carterd/BTSpecializedDisplay/src/gui/BluetoothConnection.cpp

#include "BluetoothConnection.h"
#include "MonitorSelector.h"
#include "../themes/display_theme.h"

void BluetoothConnection::tile_changed_cb(lv_event_t* event) {
    ((BluetoothConnection*)(event->user_data))->tileChangedCB(event);
}

void BluetoothConnection::refresh_cb(lv_event_t* event) {
	((BluetoothConnection*)(event->user_data))->refreshCB(event);
}

void BluetoothConnection::exit_btn_cb(lv_event_t* event) {
    ((BluetoothConnection*)(event->user_data))->exitButtonCB(event);
}

void BluetoothConnection::lv_event_encorder_cb(lv_event_t* event) {
    ((BluetoothConnection*)(event->user_data))->encoderActivityCB(event);
}

void BluetoothConnection::connecting_timer_cb(lv_timer_t * timer) {
    ((BluetoothConnection*)(timer->user_data))->connectingTimerCB(timer);
}

BluetoothConnection::BluetoothConnection(BluetoothController* bluetoothController, ConfigStore* configStore, lv_img_dsc_t* image, lv_indev_t* indev, ButtonLabelBar* buttonLabelBar)  : ButtonLabelledLvObject(indev, buttonLabelBar)
{
    this->monitor_tile_obj = NULL;
	this->bluetoothController = bluetoothController;
	this->configStore = configStore;
	this->image = image;
    this->connectedBike = false;
    this->connectedHeartRateMonitor = false;
    this->monitorSelectorActive = false;
    this->monitorSelector = NULL;
    this->exiting = false;
    this->initialConnectionState = true;
    this->connectingIncludesHeartRateMonitorState = false;
}

BluetoothConnection::~BluetoothConnection()
{
    this->monitorSelector->destroyLvObj();
    //delete(this->monitorLvObj);
    BluetoothConnection::destroyLvObj();
}

lv_obj_t* BluetoothConnection::createLvObj(lv_obj_t* parent)
{
    // get the style we'll need for the bar
    display_theme_styles_t* display_theme_styles = (display_theme_styles_t*)lv_disp_get_theme(lv_obj_get_disp(parent))->user_data;
    lv_style_t* no_scrollbar_style = &(display_theme_styles->no_scrollbar);
    lv_style_t* button_no_highlight_style = &(display_theme_styles->button_no_highlight);
    lv_style_t* searching_button_style = &(display_theme_styles->searching_label);

    // create a group for the button for exit connection
    this->group = lv_group_create();

    lv_obj_update_layout(parent);    
    this->this_obj = lv_obj_create(parent);
    lv_obj_add_style(this->this_obj, no_scrollbar_style, LV_PART_SCROLLBAR);
    lv_obj_set_size(this->this_obj, lv_obj_get_width(parent), lv_obj_get_height(parent));
    lv_obj_set_align(this->this_obj, LV_ALIGN_CENTER);

    // The connection is created from a tileview
    this->tileview_obj = lv_tileview_create(this->this_obj);
    lv_obj_add_event_cb(this->tileview_obj, BluetoothConnection::tile_changed_cb, LV_EVENT_VALUE_CHANGED, this);
    lv_obj_add_style(tileview_obj, no_scrollbar_style, LV_PART_SCROLLBAR);
    this->connection_tile_obj = lv_tileview_add_tile(tileview_obj, 0, 0, LV_DIR_ALL);
    lv_obj_add_style(this->connection_tile_obj, no_scrollbar_style, LV_PART_SCROLLBAR);

    // Create a button
    this->button_obj = lv_btn_create(this->connection_tile_obj);
    lv_obj_center(this->button_obj);
    lv_obj_add_style(this->button_obj, button_no_highlight_style, LV_PART_MAIN);
    lv_obj_add_event_cb(this->button_obj, BluetoothConnection::refresh_cb, LV_EVENT_REFRESH, this);
    lv_obj_add_event_cb(this->button_obj, BluetoothConnection::exit_btn_cb, LV_EVENT_LONG_PRESSED, this);
    lv_obj_add_event_cb(this->button_obj, BluetoothConnection::lv_event_encorder_cb, LV_EVENT_CLICKED, this);
    lv_group_add_obj(this->group, this->button_obj);
    
    // add two activity button object to identify if encoder is being used
    lv_obj_t* activity_btn_1_obj = lv_btn_create(this->this_obj);
    lv_obj_add_style(activity_btn_1_obj, button_no_highlight_style, LV_PART_MAIN);
    lv_obj_add_event_cb(activity_btn_1_obj, BluetoothConnection::lv_event_encorder_cb, LV_EVENT_FOCUSED, this);
    lv_group_add_obj(this->group, activity_btn_1_obj);

    // Associate an image
    lv_obj_t* img_obj = lv_img_create(this->button_obj);
    lv_img_set_src(img_obj, this->image);
    lv_obj_center(img_obj);

    // Associate a spinner
    this->spinner_obj = lv_spinner_create(this->this_obj, 1000, 60);
    lv_obj_center(this->spinner_obj);

    // Associate a label connecting
    this->label_obj = lv_label_create(this->this_obj);
    lv_label_set_text(this->label_obj, SEARCHING_STRING);
    lv_obj_add_style(this->label_obj, searching_button_style, LV_PART_MAIN);
    lv_obj_center(this->label_obj);
    
    // create the monitor tile
    if (this->monitorSelector) {
        this->monitor_tile_obj = lv_tileview_add_tile(this->tileview_obj, 0, 1, LV_DIR_ALL);
        lv_obj_add_style(this->monitor_tile_obj, no_scrollbar_style, LV_PART_SCROLLBAR);
    }
    
    // Return the connection lv_obj just in case
    return this->this_obj;
}

void BluetoothConnection::destroyLvObj() {
    if (this->group) lv_group_del(this->group);
    this->group = NULL;
    BaseLvObject::destroyLvObj();
}

void BluetoothConnection::focusLvObj(BaseLvObject* defocusLvObj)
{
    this->updateButtonLabelBar();

    if (defocusLvObj) {
        // We have arrived here from an external lvObject so we're on the initial connection
        this->defocusLvObj = defocusLvObj;
        this->exiting = false;
        this->initialConnectionState = true;
        this->connectingIncludesHeartRateMonitorState = false;

        // Ensure the monitor selector is started
        this->monitorSelector->destroyLvObj();
        this->monitorSelector->createLvObj(this->monitor_tile_obj);

        // Ensure the connection view is shown if jumping to the connection
        lv_obj_set_tile_id(this->tileview_obj, 0, 0, LV_ANIM_OFF);
        // Capture movement from here on in
        lv_indev_set_group(this->indev, this->group);
        lv_group_focus_obj(this->button_obj);

        this->monitorSelectorActive = false;
        this->startBikeConnection();
        
    } else {
        // If we are already connecting and we get focus this is a reconnect due to disconnect
        this->initialConnectionState = false;
        // Ensure the connection view is shown if jumping to the connection
        lv_obj_set_tile_id(this->tileview_obj, 0, 0, LV_ANIM_OFF);
        // Capture movement from here on in
        lv_indev_set_group(this->indev, this->group);
        lv_group_focus_obj(this->button_obj);

        this->monitorSelectorActive = false;
        this->startBikeConnection();
    }
}

void BluetoothConnection::setMonitorSelector(MonitorSelector* monitorSelector)
{
    this->monitorSelector = monitorSelector;
    this->monitorSelector->setBluetoothConnection(this);
}

void BluetoothConnection::startBikeConnection()
{
    this->connectingStartTime = millis();
    this->connecting_timer = lv_timer_create(connecting_timer_cb, CONNECTING_TIMEOUT_MILLIS, this);
    // We should be in a disconnected state but ensure the bike is disconnected
    this->connectedBike = false;
    this->bluetoothController->getBluetoothBike()->disconnect();
    this->connectedHeartRateMonitor = this->bluetoothController->getBluetoothHeartRateMonitor()->isConnected();
    
    this->bluetoothController->startConnections(this->button_obj);

    lv_obj_clear_flag(this->label_obj, LV_OBJ_FLAG_HIDDEN);
    lv_obj_clear_flag(this->spinner_obj, LV_OBJ_FLAG_HIDDEN);
}

void BluetoothConnection::stopBTConnection()
{
    this->connectedBike = false;
    this->connectedHeartRateMonitor = false;
    this->bluetoothController->stopConnections();
}

void BluetoothConnection::restartBTConnection() {
    //this->startBTConnection();
    this->focusLvObj();
}


void BluetoothConnection::updateButtonLabelBar() {
    if (this->buttonLabelBar) {
        this->buttonLabelBar->setButtonLabels("", LV_SYMBOL_CLOSE, "");
        this->buttonLabelBar->setAutoHide(true);
        this->hideButtonLabels();
    }
}

void BluetoothConnection::showButtonLabels() {
    if (this->buttonLabelBar) {
        this->buttonLabelBar->show();
    }
}

void BluetoothConnection::hideButtonLabels()
{
	if (this->buttonLabelBar) {
		this->buttonLabelBar->hide();
	}
}

void BluetoothConnection::switchToMonitorLvObject()
{
    // Ensure the monitor screen is set up and move the gui to showing it
    if (this->monitorSelector) {
        this->monitorSelector->setBluetoothBike(this->bluetoothController->getBluetoothBike());
        this->monitorSelector->initBluetoothStats();
        this->monitorSelector->focusLvObj(this);
        lv_obj_set_tile_id(this->tileview_obj, 0, 1, LV_ANIM_ON);
        this->monitorSelectorActive = true;
    }
}

void BluetoothConnection::switchToConnectionLvObject()
{
    // Ensure the monitor screen is set up and move the gui to showing it
    if (this->monitorSelectorActive) {
        lv_obj_set_tile_id(this->tileview_obj, 0, 0, LV_ANIM_ON);
        this->monitorSelectorActive = false;
    }
}

void BluetoothConnection::connectionSuccess() 
{
    lv_obj_add_flag(this->label_obj, LV_OBJ_FLAG_HIDDEN);
    lv_obj_add_flag(this->spinner_obj, LV_OBJ_FLAG_HIDDEN);

    // On successful connection we should ensure the bike config is set correctly
    BikeConfig bikeConfig = this->configStore->getBikeConfig();

    if (bikeConfig.beeper.managed) this->bluetoothController->getBluetoothBike()->writeBikeStateAttribute(BikeStateAttributeIndex::BEEP_ON_OFF_STATE, &(bikeConfig.beeper.value));
    //if (bikeConfig.wheelCircumference.managed) this->bluetoothController->getBluetoothBike()->writeBikeStateAttribute(BikeStateAttributeIndex::WHEEL_CIRCUMFERENCE, &(bikeConfig.wheelCircumference.value));
    if (bikeConfig.supportAssistLevels.managed) this->bluetoothController->getBluetoothBike()->writeBikeStateAttribute(BikeStateAttributeIndex::SUPPORT_ASSIST_LEVELS, &(bikeConfig.supportAssistLevels.value));
    if (bikeConfig.peakPowerAssistLevels.managed) this->bluetoothController->getBluetoothBike()->writeBikeStateAttribute(BikeStateAttributeIndex::PEAK_POWER_ASSIST_LEVELS, &(bikeConfig.peakPowerAssistLevels.value));
    
    // Ensure the monitor screen is set up and move the gui to showing it
    this->switchToMonitorLvObject();
}

void BluetoothConnection::checkForConnection() {  
    if (this->bluetoothController->checkForConnections(&this->configStore->getBTAddressesConfig(), this->configStore->getDisplayConfig().connectBatteryOnly)) {
        if (!this->connectedBike && this->bluetoothController->getBluetoothBike()->isConnected()) {
            // The referesh is now going to connect into the monitored panel(s)
            this->connectedBike = true;
            this->connectionSuccess();
        }
        if (!this->connectedHeartRateMonitor && this->bluetoothController->getBluetoothHeartRateMonitor()->isConnected()) {            
            // If we're riding with 
            this->connectedHeartRateMonitor = true;
            this->connectingIncludesHeartRateMonitorState = true;
        }
    }
}

void BluetoothConnection::checkForConnectedUpdates() {
    if (this->connectedBike) {
        // Check that the BT connection is still there
        if (this->bluetoothController->getBluetoothBike()->isConnected()) {
            // We are begin refereshed by the connection now
            this->monitorSelector->statusUpdate();
        }        
        else {
            // If the BT connection has gone down then we need to attempt to re-establish
            this->restartBTConnection();
            return;
        }
    }
    if (this->connectedHeartRateMonitor && !this->bluetoothController->getBluetoothHeartRateMonitor()->isConnected()) {
        // represents the identification of loss of Heart rate monitor
        this->connectedHeartRateMonitor = false;
        this->bluetoothController->startConnections(this->button_obj);    
    }
}

void BluetoothConnection::refreshCB(lv_event_t* event)
{
    this->checkForConnection();
    this->checkForConnectedUpdates();
}

void BluetoothConnection::exitButtonCB(lv_event_t* event)
{
    this->exiting = true;
    // Check which screen is being shown if we're on the wrong screen then perform switch to exit screen
    if (this->monitorSelectorActive) {        
        this->switchToConnectionLvObject();
        return;
    }

    if (this->defocusLvObj) {
        this->defocusLvObj->focusLvObj();
        this->stopBTConnection();
        this->monitorSelector->destroyLvObj();
    }
}

void BluetoothConnection::tileChangedCB(lv_event_t* event)
{
    this->monitorSelectorActive = lv_tileview_get_tile_act(this->tileview_obj) != this->connection_tile_obj;
    if (this->exiting) this->exitButtonCB(event);
}

void BluetoothConnection::encoderActivityCB(lv_event_t* event)
{
    this->showButtonLabels();    
    lv_group_focus_obj(this->button_obj);
}

void BluetoothConnection::connectingTimerCB(lv_timer_t* timer) 
{
    if (this->connecting_timer == timer) {
        if (!this->connectedBike) {
            // No bike after timeout then quit looking for bike
            this->exitButtonCB();
        }
        else {
            // We've connected to the bike ... do we need to keep scanning for heart rate monitor
            if (!this->connectingIncludesHeartRateMonitorState)                
                this->bluetoothController->stopScanning();
        }
    }
}
