carterd/BTSpecializedDisplay/src/gui/monitors/small/BaseMonitorSmall.cpp

    #include "BaseMonitorSmall.h"

    lv_style_t* BaseMonitorSmall::getMonitorPanelStyle(display_theme_styles_t* display_theme_styles) {
        return &(display_theme_styles->small_monitor_panel);
    }
